cybbkru/Anemometer/Image gallery/20230528_162417.jpg

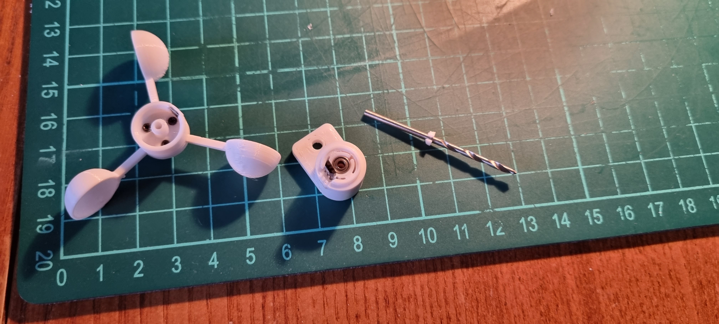
Image gallery/20230528_162417.jpg
