cybbkru/Anemometer/Image gallery/20230528_182359.jpg

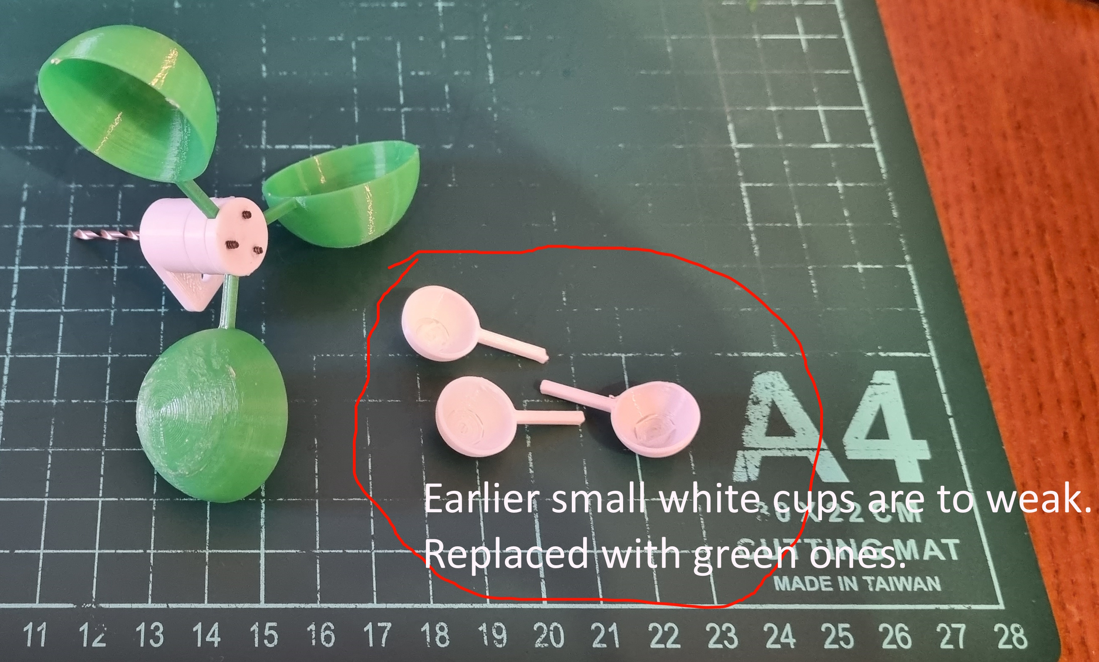
Image gallery/20230528_182359.jpg
