cybbkru/Anemometer/Image gallery/20230602_174426.jpg

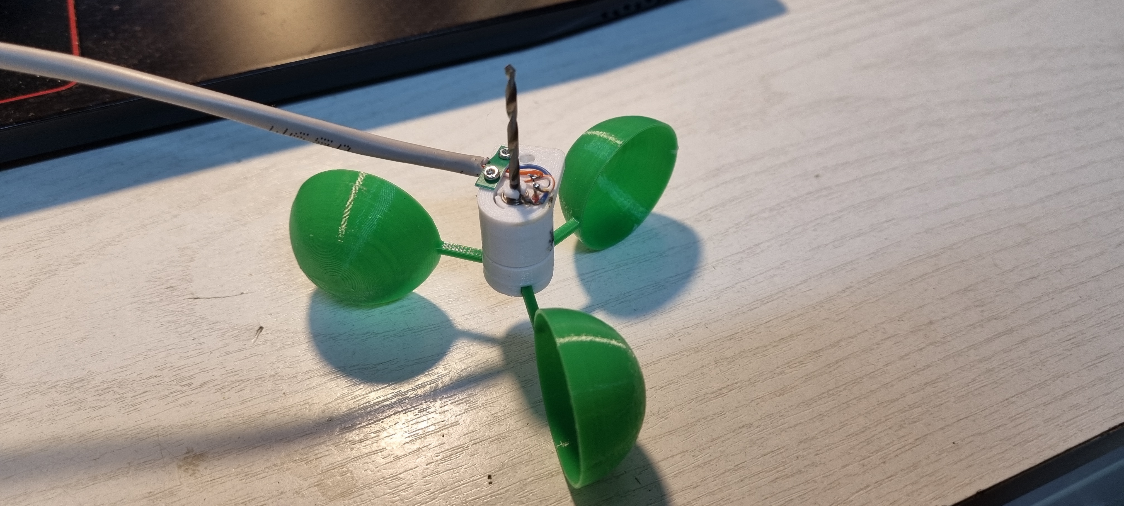
Image gallery/20230602_174426.jpg
