cybbkru/Anemometer/Image gallery/20230602_175223.jpg

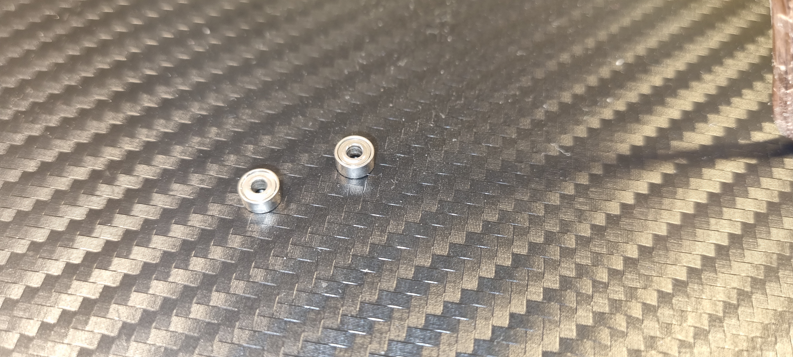
Image gallery/20230602_175223.jpg
