cybbkru/Anemometer/Image gallery/20230602_175314.jpg

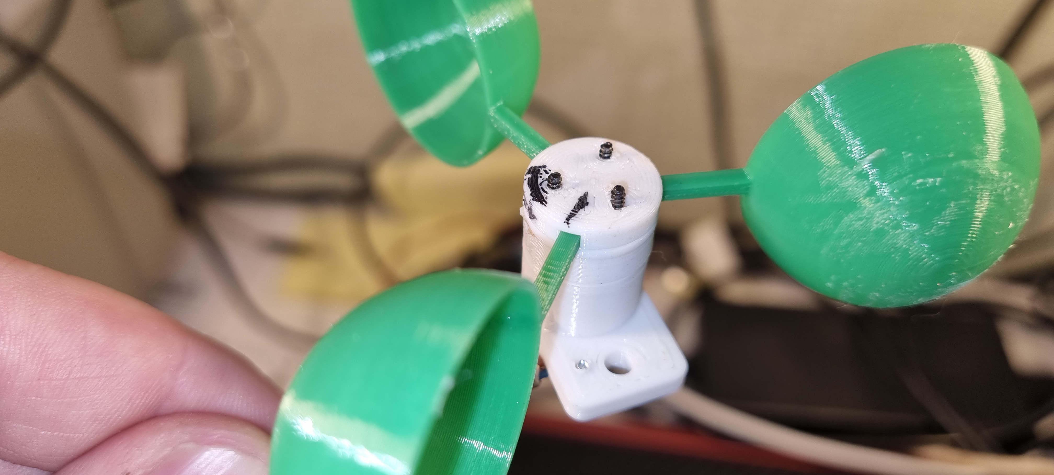
Image gallery/20230602_175314.jpg
