cybbkru/Anemometer/Image gallery/20230602_175317.jpg

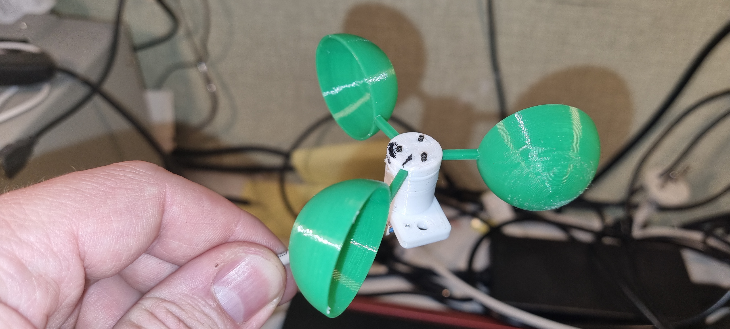
Image gallery/20230602_175317.jpg
