cybbkru/Anemometer/Image gallery/20230602_175323.jpg

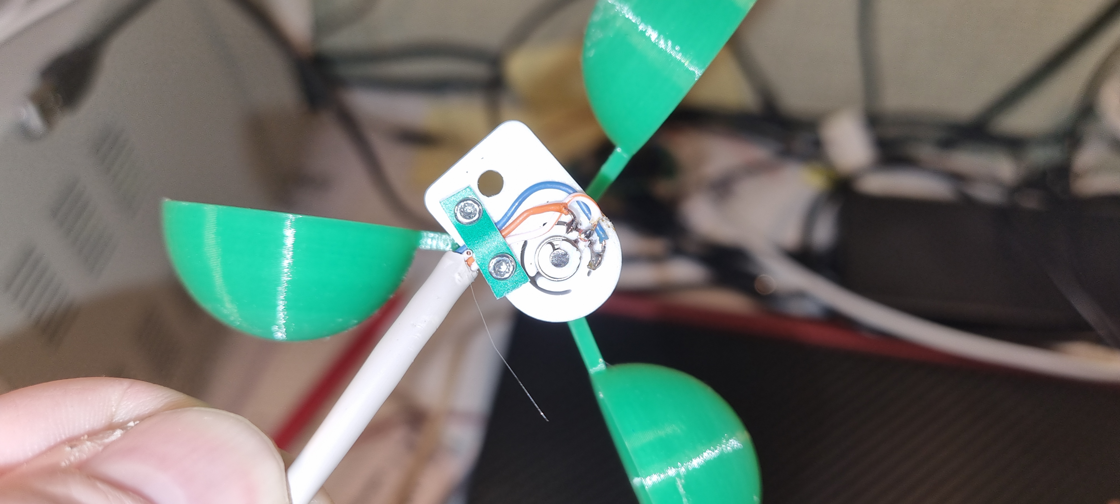
Image gallery/20230602_175323.jpg
