cybbkru/Anemometer/Image gallery/20230602_181718.jpg

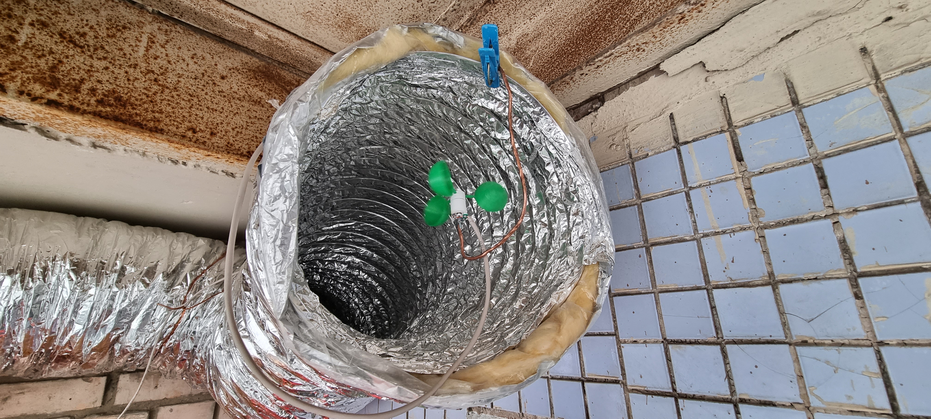
Image gallery/20230602_181718.jpg
